oizom-iot/airowl/Firmware/md_images/image-1.png

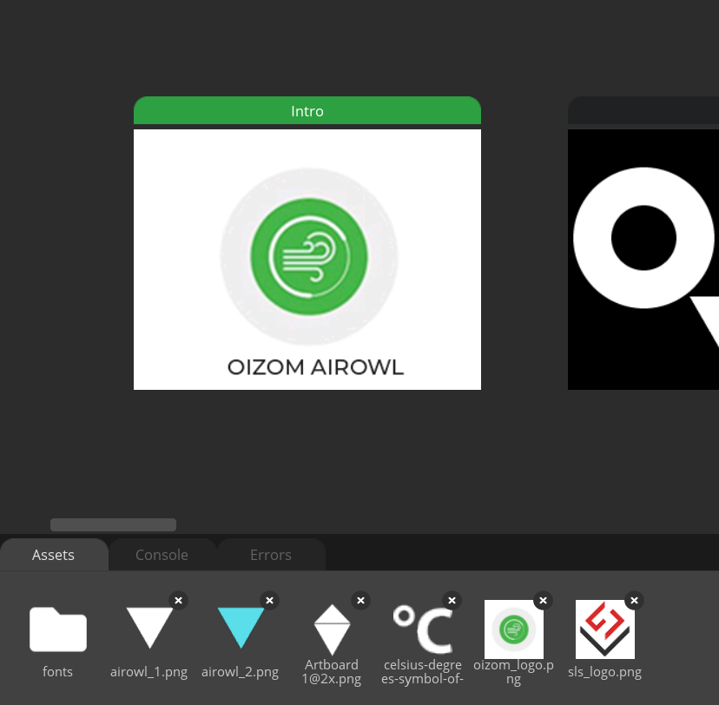
Firmware/md_images/image-1.png
