oizom-iot/airowl/Mountingboard/AirOwl_v1/Renders/AirOwl_2.png

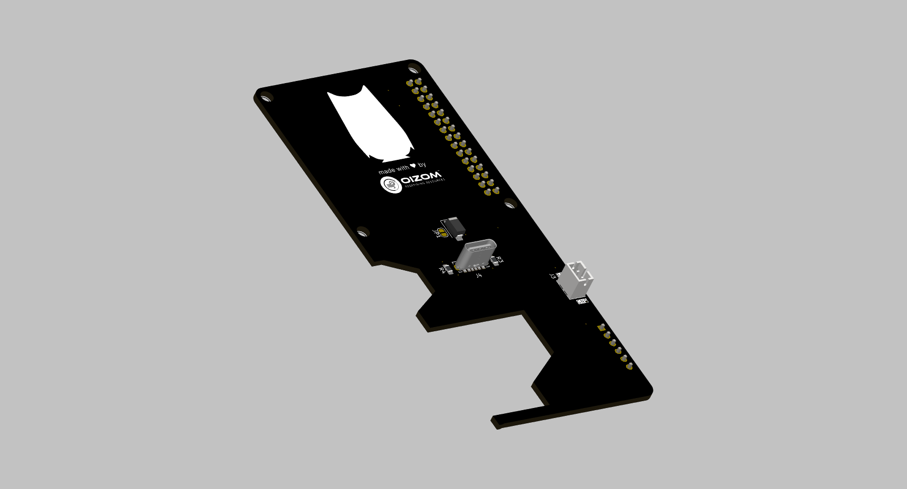
Mountingboard/AirOwl_v1/Renders/AirOwl_2.png
